PCARS/PCARS_Band_Display/Reference Docs/ESP32-Devkit_Pinout.PNG

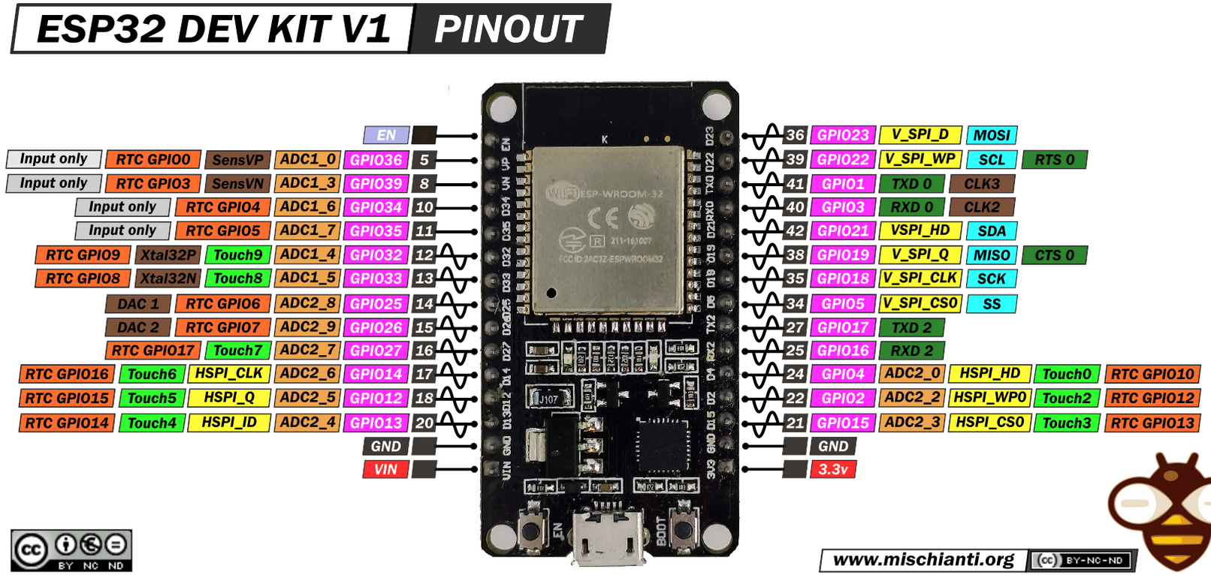
Reference Docs/ESP32-Devkit_Pinout.PNG
