PCARS/PCARS_Band_Display/Reference Docs/ICOM-7300/icom civ cable.jpg

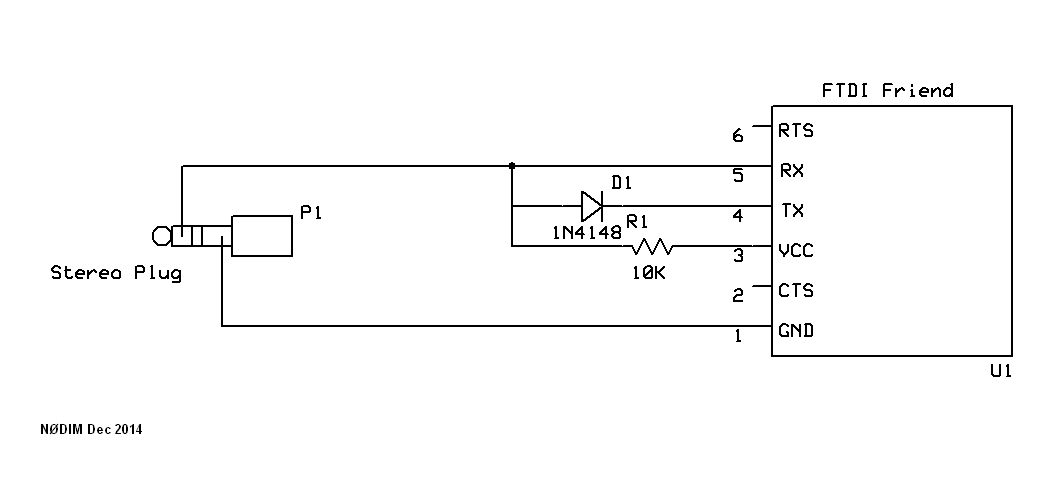
Reference Docs/ICOM-7300/icom civ cable.jpg
